ikuto0815/eink_mahjong_compass/pcb/EASYEDA_MODELS/FC-135R_L3.2-W1.5.step

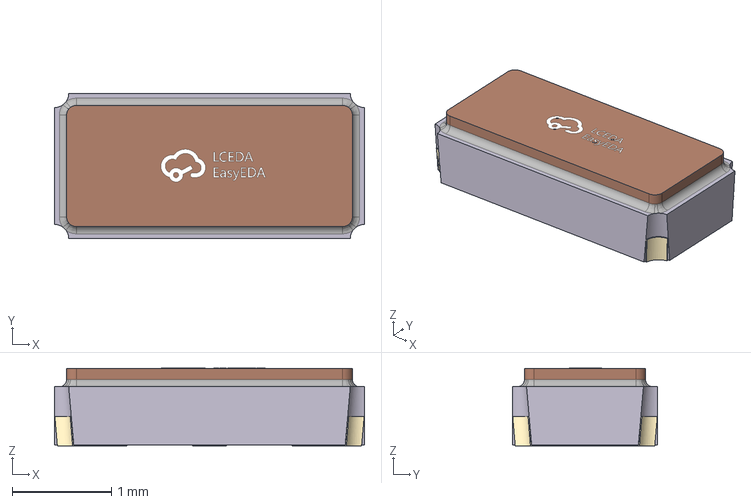
[picture p23: CAD file, 2026-01-20]
pcb/EASYEDA_MODELS/FC-135R_L3.2-W1.5.step
3.13 x 1.47 x 0.783 mm
