ikuto0815/eink_mahjong_compass/pcb/EASYEDA_MODELS/WIFIM-SMD_ESP32-S3-WROOM-1-N8.step

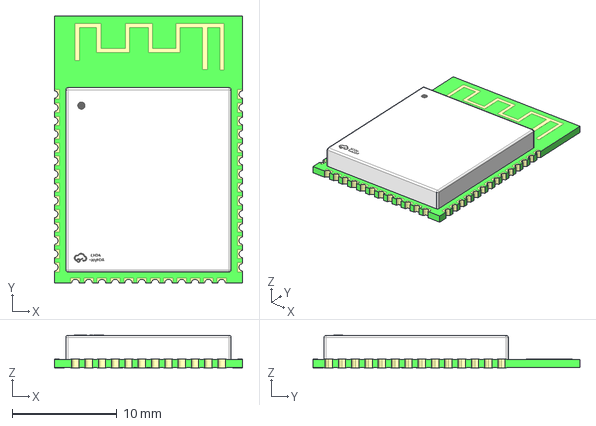
[picture p24: CAD file, 2026-01-20]
pcb/EASYEDA_MODELS/WIFIM-SMD_ESP32-S3-WROOM-1-N8.step
18.0 x 25.5 x 3.12 mm
