ikuto0815/eink_mahjong_compass/pcb/EASYEDA_MODELS/SOT-23-3L_L2.9-W1.6-H1.1-LS2.8-P0.95.step

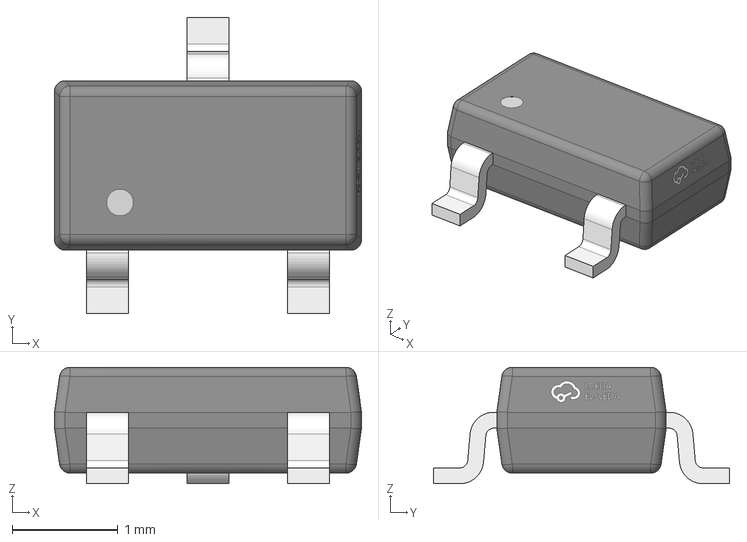
[picture p25: CAD file, 2026-01-20]
pcb/EASYEDA_MODELS/SOT-23-3L_L2.9-W1.6-H1.1-LS2.8-P0.95.step
2.90 x 2.80 x 1.10 mm
