ikuto0815/eink_mahjong_compass/pcb/EASYEDA_MODELS/SMA_L4.3-W2.6-LS5.1-RD.step

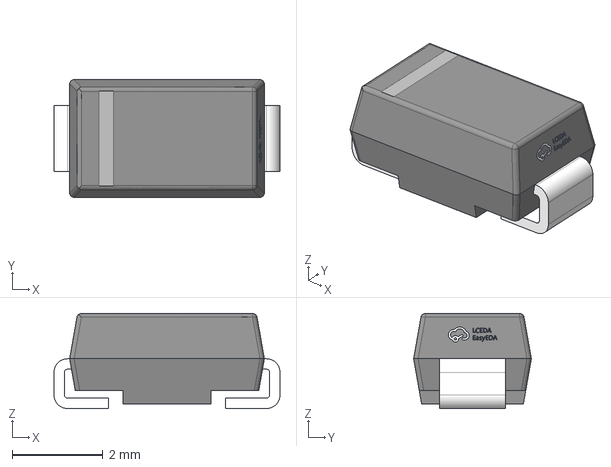
[picture p26: CAD file, 2026-01-20]
pcb/EASYEDA_MODELS/SMA_L4.3-W2.6-LS5.1-RD.step
4.99 x 2.60 x 2.10 mm
