ikuto0815/eink_mahjong_compass/pcb/EASYEDA_MODELS/ESOP-8_L4.9-W3.9-H1.6-LS6.0-P1.27.step

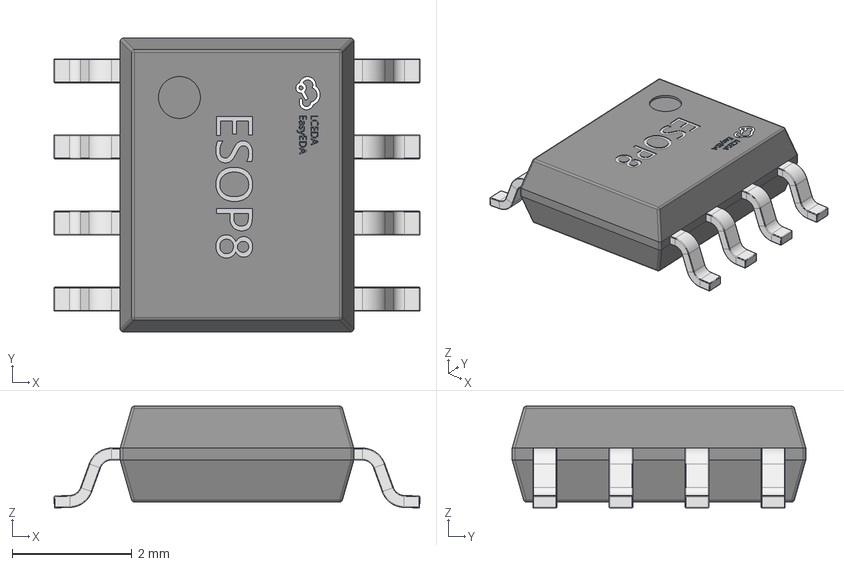
[picture p27: CAD file, 2026-01-20]
pcb/EASYEDA_MODELS/ESOP-8_L4.9-W3.9-H1.6-LS6.0-P1.27.step
6.11 x 4.90 x 1.70 mm
