ikuto0815/eink_mahjong_compass/pcb/EASYEDA_MODELS/USB-C-SMD_HYCW498-USBC16-735B.step

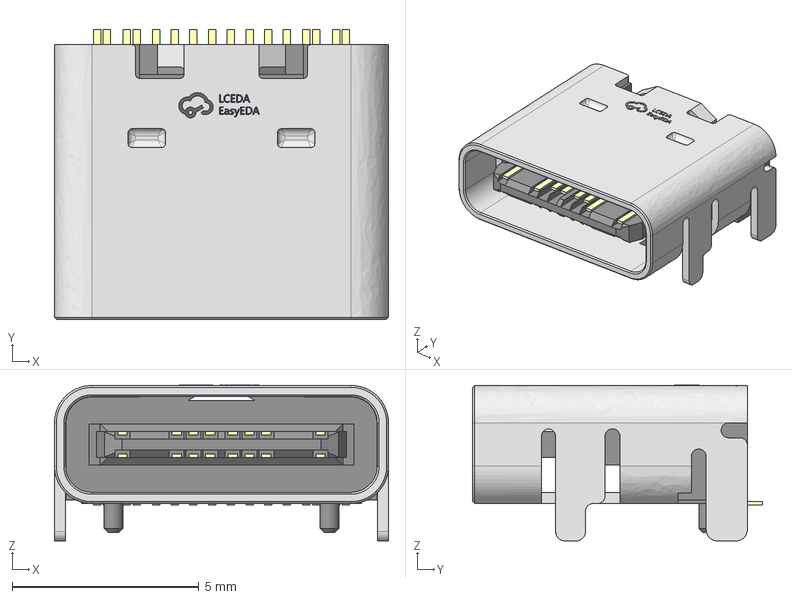
[picture p28: CAD file, 2026-01-20]
pcb/EASYEDA_MODELS/USB-C-SMD_HYCW498-USBC16-735B.step
8.94 x 7.75 x 4.17 mm
