ikuto0815/eink_mahjong_compass/pcb/EASYEDA_MODELS/SOT-89-3_L4.3-W2.5-H1.6-LS4.1-P1.50.step

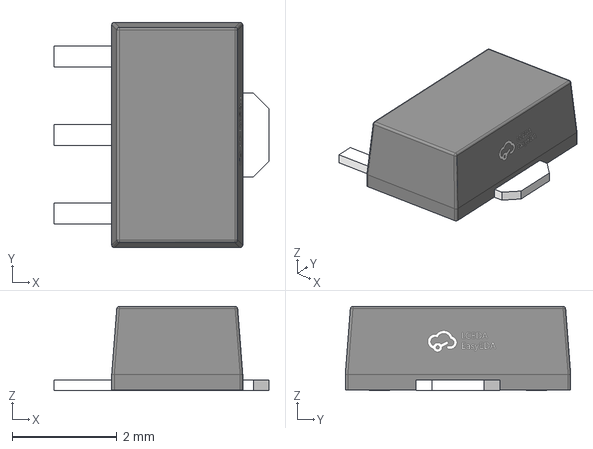
[picture p29: CAD file, 2026-01-20]
pcb/EASYEDA_MODELS/SOT-89-3_L4.3-W2.5-H1.6-LS4.1-P1.50.step
4.10 x 4.30 x 1.61 mm
