ikuto0815/eink_mahjong_compass/pcb/EASYEDA_MODELS/SOT-23-5_L2.9-W1.6-P0.95-LS2.8-BR.step

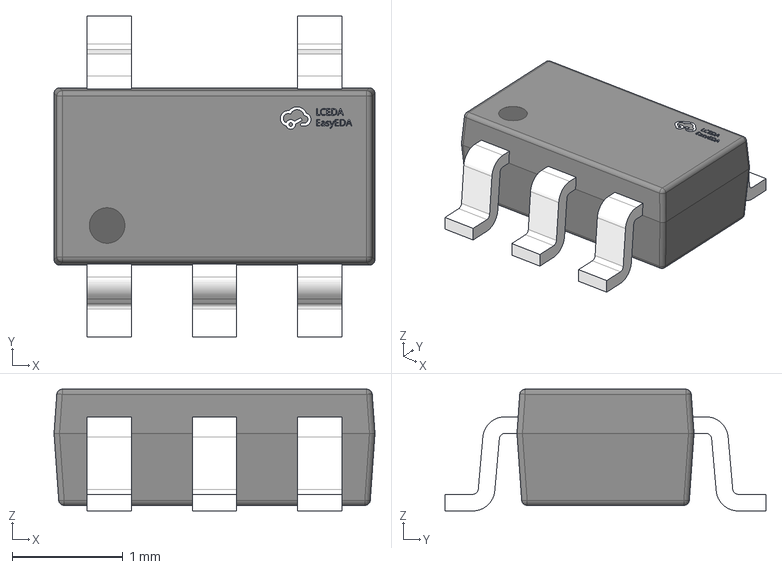
[picture p30: CAD file, 2026-01-20]
pcb/EASYEDA_MODELS/SOT-23-5_L2.9-W1.6-P0.95-LS2.8-BR.step
2.90 x 2.90 x 1.10 mm
