ikuto0815/eink_mahjong_compass/pcb/EASYEDA_MODELS/TYPE-C-SMD_6P-L8.9-W6.8-H3.2-P1.00.step

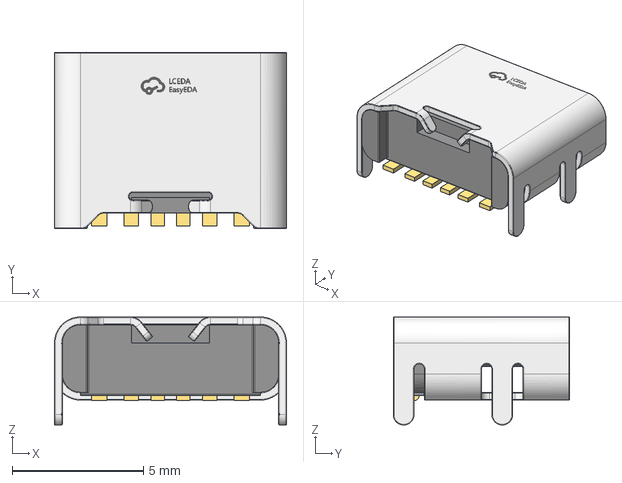
[picture p31: CAD file, 2026-01-20]
pcb/EASYEDA_MODELS/TYPE-C-SMD_6P-L8.9-W6.8-H3.2-P1.00.step
8.84 x 6.72 x 4.11 mm
