ikuto0815/eink_mahjong_compass/pcb/EASYEDA_MODELS/C0402_L1.0-W0.5-H0.5.step

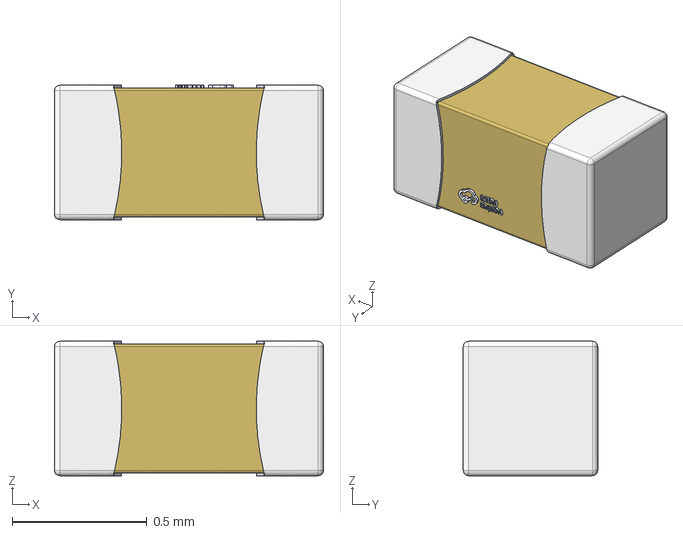
[picture p32: CAD file, 2026-01-20]
pcb/EASYEDA_MODELS/C0402_L1.0-W0.5-H0.5.step
1.00 x 0.5 x 0.5 mm
