ikuto0815/eink_mahjong_compass/pcb/EASYEDA_MODELS/SOT-353-5P_L2.0-W1.3-H1.1-LS2.0-P0.65.step

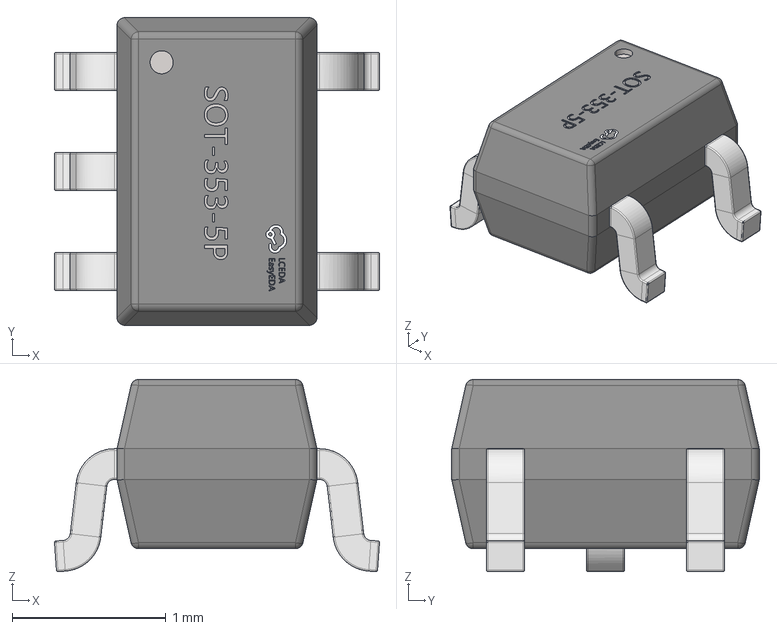
[picture p33: CAD file, 2026-01-20]
pcb/EASYEDA_MODELS/SOT-353-5P_L2.0-W1.3-H1.1-LS2.0-P0.65.step
2.11 x 2.00 x 1.25 mm
