ikuto0815/eink_mahjong_compass/pcb/EASYEDA_MODELS/SOT-23-6_L2.9-W1.6-P0.95-LS2.9-BL.step

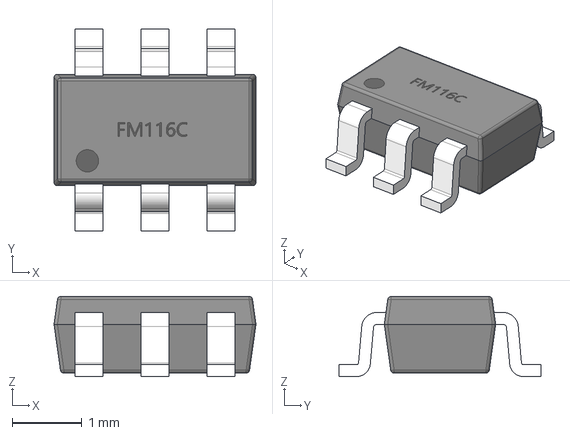
[picture p34: CAD file, 2026-01-20]
pcb/EASYEDA_MODELS/SOT-23-6_L2.9-W1.6-P0.95-LS2.9-BL.step
2.90 x 2.90 x 1.15 mm
