ikuto0815/eink_mahjong_compass/pcb/EASYEDA_MODELS/TSOT-23-5_L2.9-W1.6-H1.00-LS2.8-P0.95.step

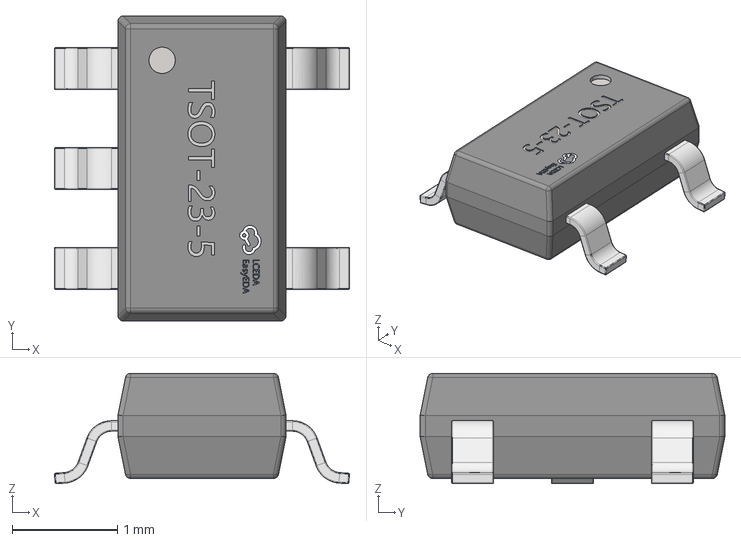
[picture p35: CAD file, 2026-01-20]
pcb/EASYEDA_MODELS/TSOT-23-5_L2.9-W1.6-H1.00-LS2.8-P0.95.step
2.81 x 2.90 x 1.05 mm
