ikuto0815/eink_mahjong_compass/pcb/EASYEDA_MODELS/SW-SMD_4P-L5.1-W5.1-P3.70-LS6.5-TL_H1.5.step

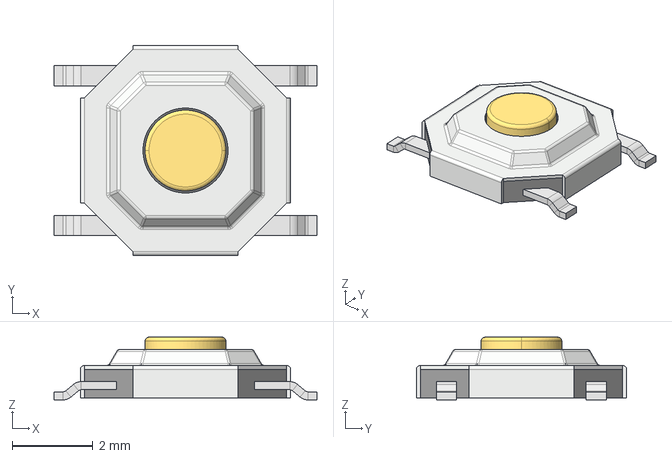
[picture p36: CAD file, 2026-01-20]
pcb/EASYEDA_MODELS/SW-SMD_4P-L5.1-W5.1-P3.70-LS6.5-TL_H1.5.step
6.50 x 5.20 x 1.55 mm
