ikuto0815/eink_mahjong_compass/pcb/EASYEDA_MODELS/WIRELM-SMD_ESP32-S3-WROOM-1U.step

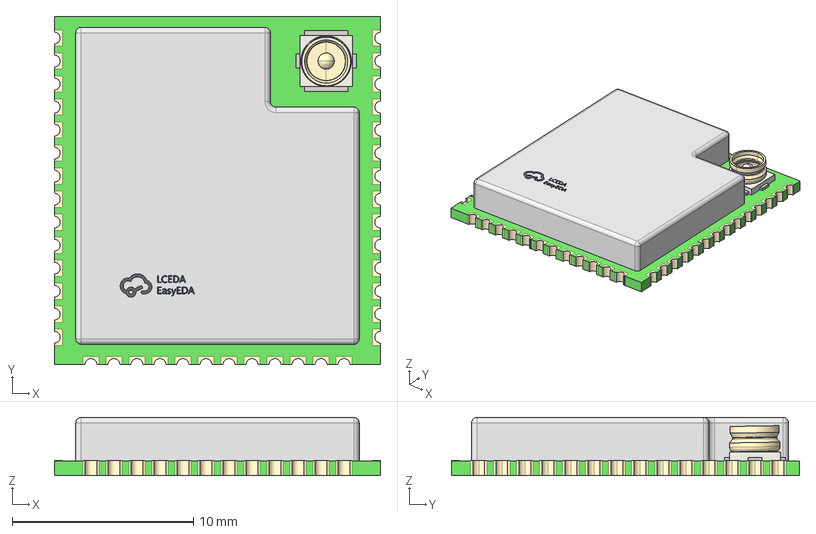
[picture p37: CAD file, 2026-01-20]
pcb/EASYEDA_MODELS/WIRELM-SMD_ESP32-S3-WROOM-1U.step
18.0 x 19.2 x 3.21 mm
