ikuto0815/eink_mahjong_compass/firmware/include/display.h

#ifndef DISPLAY_H_
#define DISPLAY_H_

void init_display(void);

void update_game_screen(bool full_update = false);
void show_connect_screen(void);
void show_standby_screen(void);

#endif // DISPLAY_H_
