ikuto0815/eink_mahjong_compass/firmware/include/io.h

#ifndef IO_H_
#define IO_H_

#include <inttypes.h>

void init_io(void);
void enable_touch_wakeup_pin(void);

void set_led(int led, int state);
void set_leds(int state);

uint32_t get_battery_voltage(void);

#endif // IO_H_
